aadeelnrx/DaVinciDriver/doc/pictures/Car_Prototype1_Top.JPG

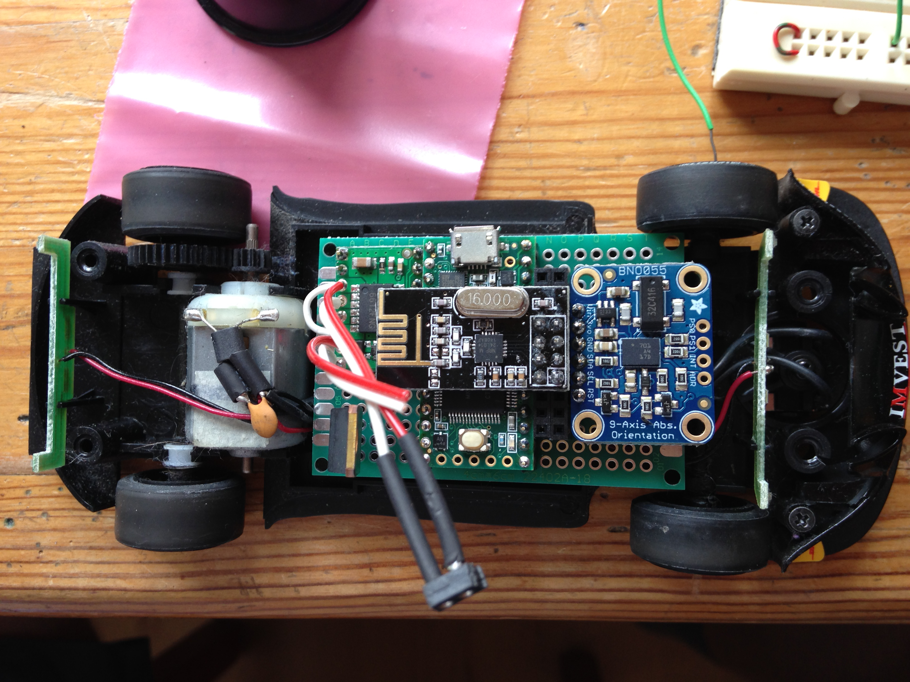
doc/pictures/Car_Prototype1_Top.JPG
