aadeelnrx/DaVinciDriver/doc/pictures/Car_Prototype2_TopSide.JPG

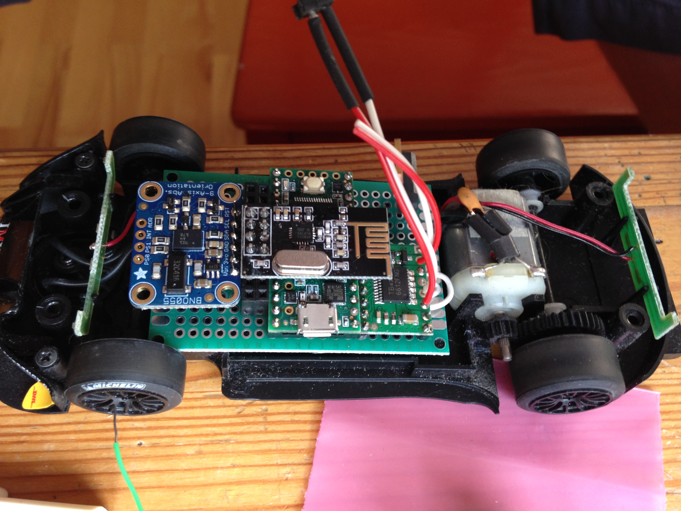
doc/pictures/Car_Prototype2_TopSide.JPG
