aadeelnrx/DaVinciDriver/doc/pictures/Teensy_31_Diode.JPG

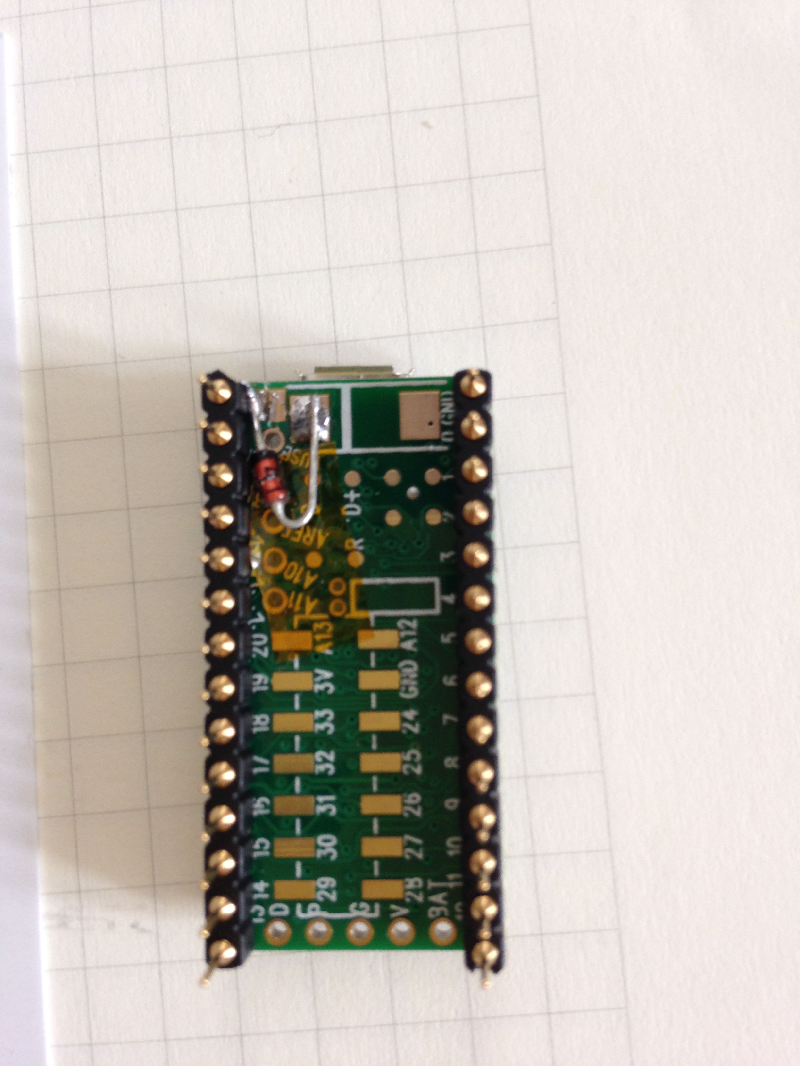
doc/pictures/Teensy_31_Diode.JPG
