aadeelnrx/DaVinciDriver/doc/Misc/accel-test-2-pwm-80-2.csv

Millis | ExTime | Distance | Speed | Acc_x | Acc_y | TrackVolt
10601 | 0 | 0 | 0 | 0.00 | 0.00 | 403
10621 | 0 | 1 | 1 | 0.00 | 0.00 | 415
10641 | 0 | 1 | 0 | 0.00 | 0.00 | 416
10661 | 0 | 2 | 1 | 0.00 | 0.00 | 408
10681 | 0 | 3 | 1 | 0.00 | 0.00 | 406
10701 | 0 | 6 | 3 | 0.00 | 0.00 | 394
10721 | 0 | 9 | 3 | 0.00 | 0.00 | 410
10741 | 0 | 13 | 4 | 0.00 | 0.00 | 404
10761 | 0 | 18 | 5 | 0.00 | 0.00 | 408
10781 | 0 | 24 | 6 | 0.00 | 0.00 | 406
10801 | 0 | 30 | 6 | 0.00 | 0.00 | 401
10821 | 0 | 37 | 7 | 0.00 | 0.00 | 405
10841 | 0 | 45 | 8 | 0.00 | 0.00 | 408
10861 | 0 | 54 | 9 | 0.00 | 0.00 | 407
10881 | 0 | 63 | 9 | 0.00 | 0.00 | 403
10901 | 0 | 72 | 9 | 0.00 | 0.00 | 404
10921 | 0 | 82 | 10 | 0.00 | 0.00 | 403
10941 | 0 | 93 | 11 | 0.00 | 0.00 | 399
10961 | 0 | 104 | 11 | 0.00 | 0.00 | 396
10981 | 0 | 116 | 12 | 0.00 | 0.00 | 394
11001 | 0 | 128 | 12 | 0.00 | 0.00 | 386
11021 | 0 | 141 | 13 | 0.00 | 0.00 | 391
11041 | 0 | 154 | 13 | 0.00 | 0.00 | 390
11061 | 0 | 167 | 13 | 0.00 | 0.00 | 388
11081 | 1 | 181 | 14 | -0.74 | -0.75 | 387
11101 | 1 | 196 | 15 | 1.87 | -0.54 | 406
11121 | 1 | 210 | 14 | -2.24 | -0.12 | 384
11141 | 1 | 226 | 16 | 1.35 | -0.82 | 396
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
