aadeelnrx/DaVinciDriver/doc/Misc/accel-test-2-pwm-80.csv

Millis | ExTime | Distance | Speed | Acc_x | Acc_y | TrackVolt
5601 | 0 | 0 | 0 | 0.00 | 0.00 | 394
5621 | 0 | 0 | 0 | 0.00 | 0.00 | 402
5641 | 0 | 0 | 0 | 0.00 | 0.00 | 403
5661 | 0 | 1 | 1 | 0.00 | 0.00 | 391
5681 | 0 | 2 | 1 | 0.00 | 0.00 | 390
5701 | 0 | 3 | 1 | 0.00 | 0.00 | 388
5721 | 0 | 6 | 3 | 0.00 | 0.00 | 385
5741 | 0 | 8 | 2 | 0.00 | 0.00 | 382
5761 | 0 | 12 | 4 | 0.00 | 0.00 | 380
5781 | 0 | 16 | 4 | 0.00 | 0.00 | 403
5801 | 0 | 22 | 6 | 0.00 | 0.00 | 408
5821 | 0 | 28 | 6 | 0.00 | 0.00 | 411
5841 | 0 | 35 | 7 | 0.00 | 0.00 | 410
5861 | 0 | 42 | 7 | 0.00 | 0.00 | 412
5881 | 0 | 50 | 8 | 0.00 | 0.00 | 412
5901 | 0 | 58 | 8 | 0.00 | 0.00 | 407
5921 | 0 | 67 | 9 | 0.00 | 0.00 | 408
5941 | 0 | 77 | 10 | 0.00 | 0.00 | 405
5961 | 0 | 88 | 11 | 0.00 | 0.00 | 408
5981 | 0 | 99 | 11 | 0.00 | 0.00 | 407
6001 | 0 | 111 | 12 | 0.00 | 0.00 | 408
6021 | 0 | 123 | 12 | 0.00 | 0.00 | 410
6041 | 0 | 136 | 13 | 0.00 | 0.00 | 410
6061 | 0 | 150 | 14 | 0.00 | 0.00 | 409
6081 | 1 | 164 | 14 | 1.31 | -0.48 | 405
6101 | 1 | 178 | 14 | -0.35 | -1.62 | 408
6121 | 1 | 193 | 15 | -0.81 | -1.49 | 403
6141 | 1 | 208 | 15 | 0.78 | -0.02 | 403
6161 | 1 | 224 | 16 | -2.76 | 0.09 | 407
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
