aadeelnrx/DaVinciDriver/doc/Misc/accel-test-3-pwm-128-2.csv

Millis | ExTime | Distance | Speed | Acc_x | Acc_y | TrackVolt
10601 | 0 | 0 | 0 | 0.00 | 0.00 | 366
10621 | 0 | 2 | 2 | 0.00 | 0.00 | 378
10641 | 0 | 4 | 2 | 0.00 | 0.00 | 385
10661 | 0 | 8 | 4 | 0.00 | 0.00 | 385
10681 | 0 | 13 | 5 | 0.00 | 0.00 | 371
10701 | 0 | 20 | 7 | 0.00 | 0.00 | 374
10721 | 0 | 28 | 8 | 0.00 | 0.00 | 375
10741 | 0 | 37 | 9 | 0.00 | 0.00 | 369
10761 | 0 | 47 | 10 | 0.00 | 0.00 | 369
10781 | 0 | 60 | 13 | 0.00 | 0.00 | 370
10801 | 0 | 73 | 13 | 0.00 | 0.00 | 362
10821 | 0 | 87 | 14 | 0.00 | 0.00 | 365
10841 | 0 | 102 | 15 | 0.00 | 0.00 | 366
10861 | 0 | 119 | 17 | 0.00 | 0.00 | 369
10881 | 0 | 136 | 17 | 0.00 | 0.00 | 368
10901 | 0 | 153 | 17 | 0.00 | 0.00 | 367
10921 | 0 | 173 | 20 | 0.00 | 0.00 | 362
10941 | 0 | 193 | 20 | 0.00 | 0.00 | 367
10961 | 0 | 214 | 21 | 0.00 | 0.00 | 369
10981 | 0 | 236 | 22 | 0.00 | 0.00 | 356
11001 | 0 | 259 | 23 | 0.00 | 0.00 | 362
11021 | 0 | 283 | 24 | 0.00 | 0.00 | 363
11041 | 0 | 308 | 25 | 0.00 | 0.00 | 363
11061 | 0 | 333 | 25 | 0.00 | 0.00 | 380
11081 | 1 | 358 | 25 | -1.90 | -2.83 | 365
11101 | 1 | 385 | 27 | 2.29 | -1.44 | 365
11121 | 1 | 412 | 27 | 0.24 | -1.58 | 362
11141 | 1 | 439 | 27 | 0.68 | 0.42 | 363
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
