aadeelnrx/DaVinciDriver/doc/Misc/PID_Measurements/CapturePID_15_1_0.JPG

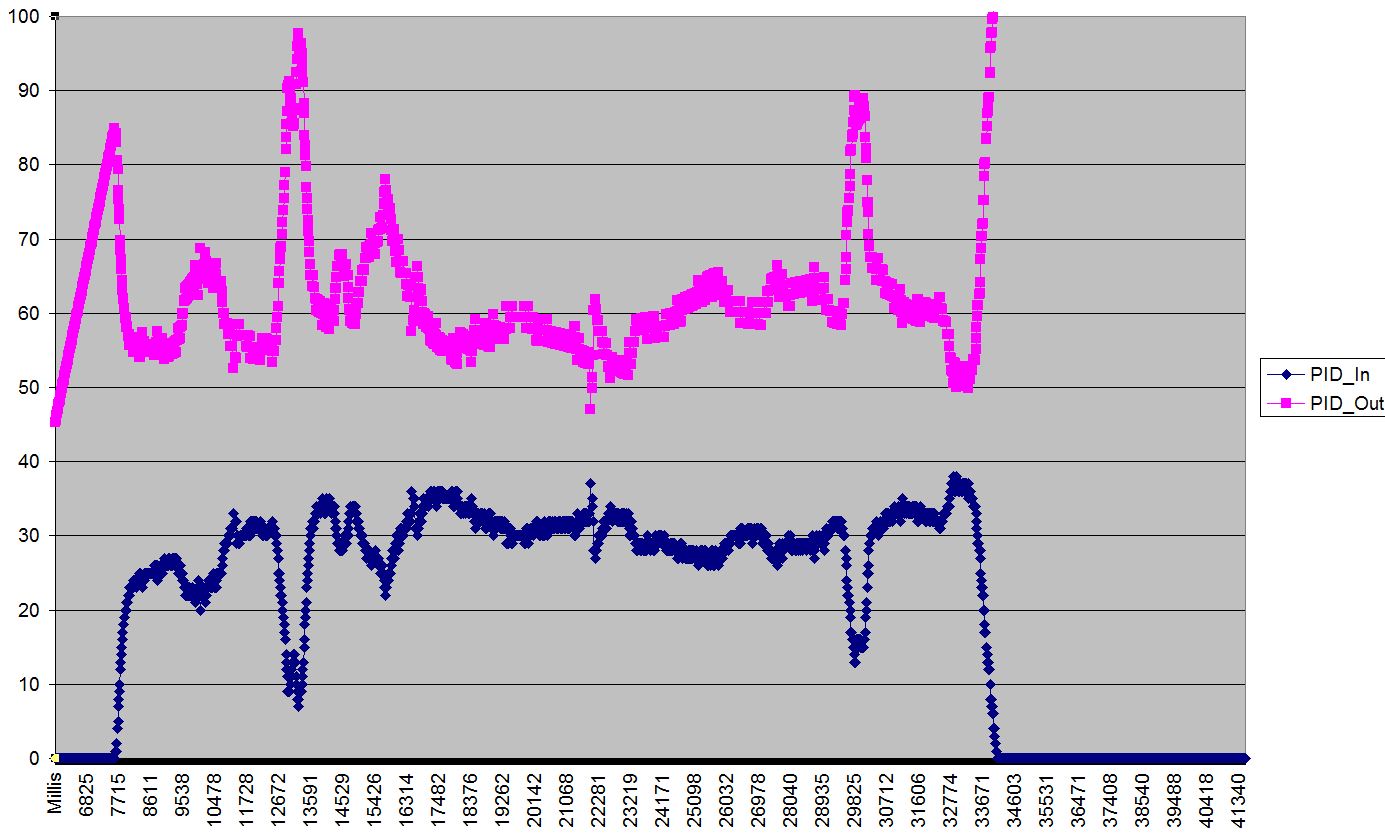
doc/Misc/PID_Measurements/CapturePID_15_1_0.JPG
