aadeelnrx/DaVinciDriver/doc/Misc/PID_Measurements/CapturePID_25_2_0.JPG

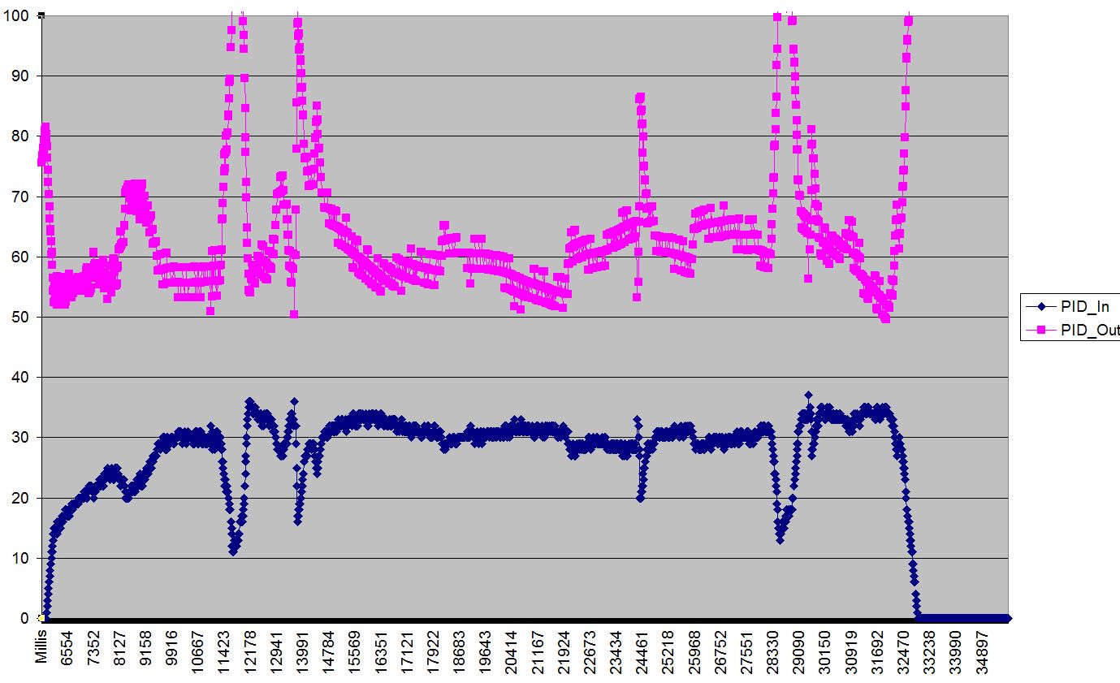
doc/Misc/PID_Measurements/CapturePID_25_2_0.JPG
