aadeelnrx/DaVinciDriver/doc/Misc/PID_Measurements/CapturePID_25_5_0.JPG

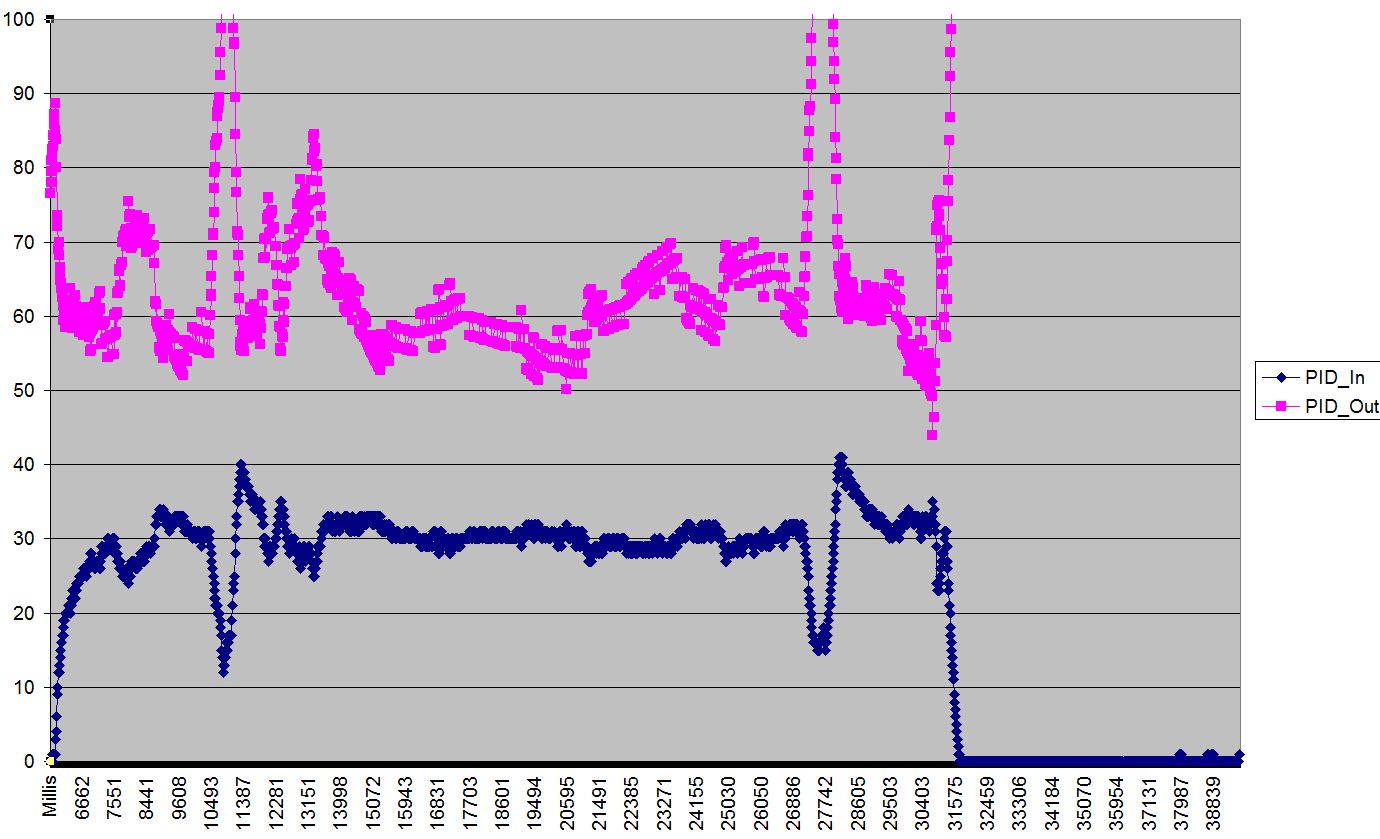
doc/Misc/PID_Measurements/CapturePID_25_5_0.JPG
