aadeelnrx/DaVinciDriver/doc/Misc/PID_Measurements/CapturePID_25_10_0001.JPG

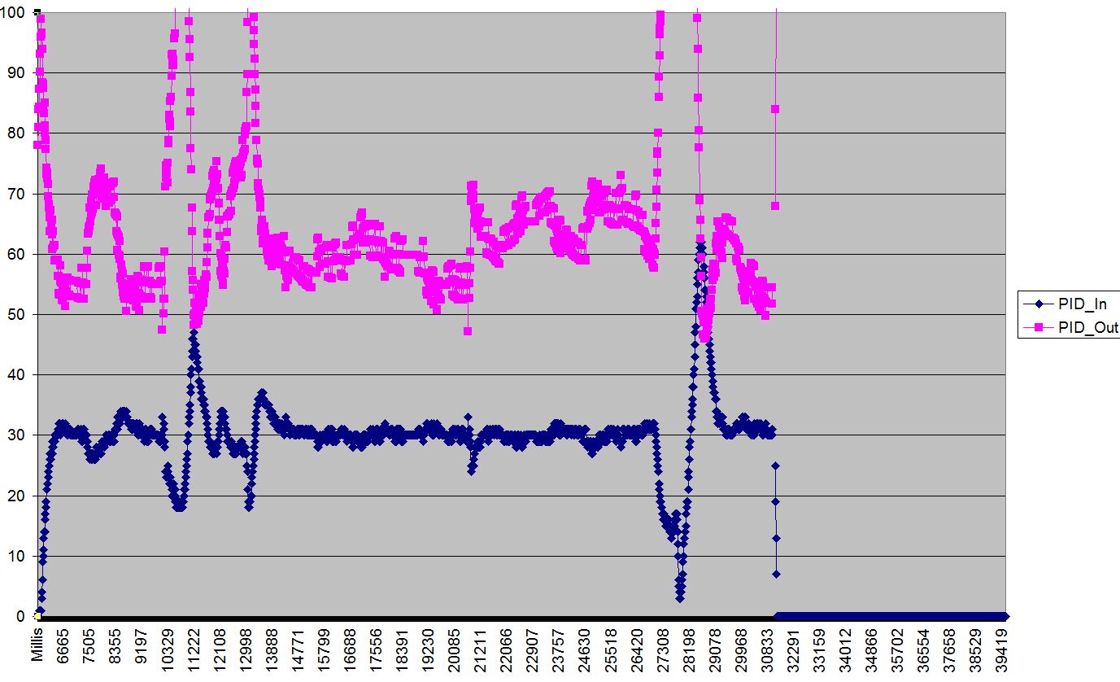
doc/Misc/PID_Measurements/CapturePID_25_10_0001.JPG
