aadeelnrx/DaVinciDriver/doc/Misc/PID_Measurements/CapturePID_25_10_01.JPG

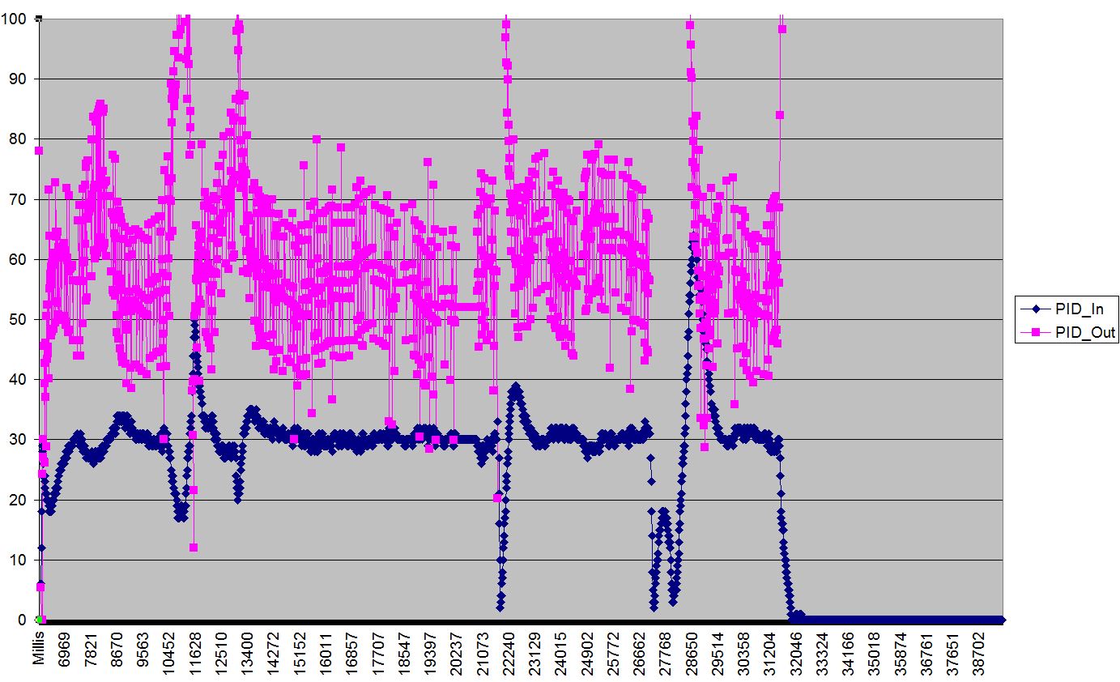
doc/Misc/PID_Measurements/CapturePID_25_10_01.JPG
