aadeelnrx/DaVinciDriver/doc/Misc/PID_Measurements/CapturePID_075_1_001_30ms.JPG

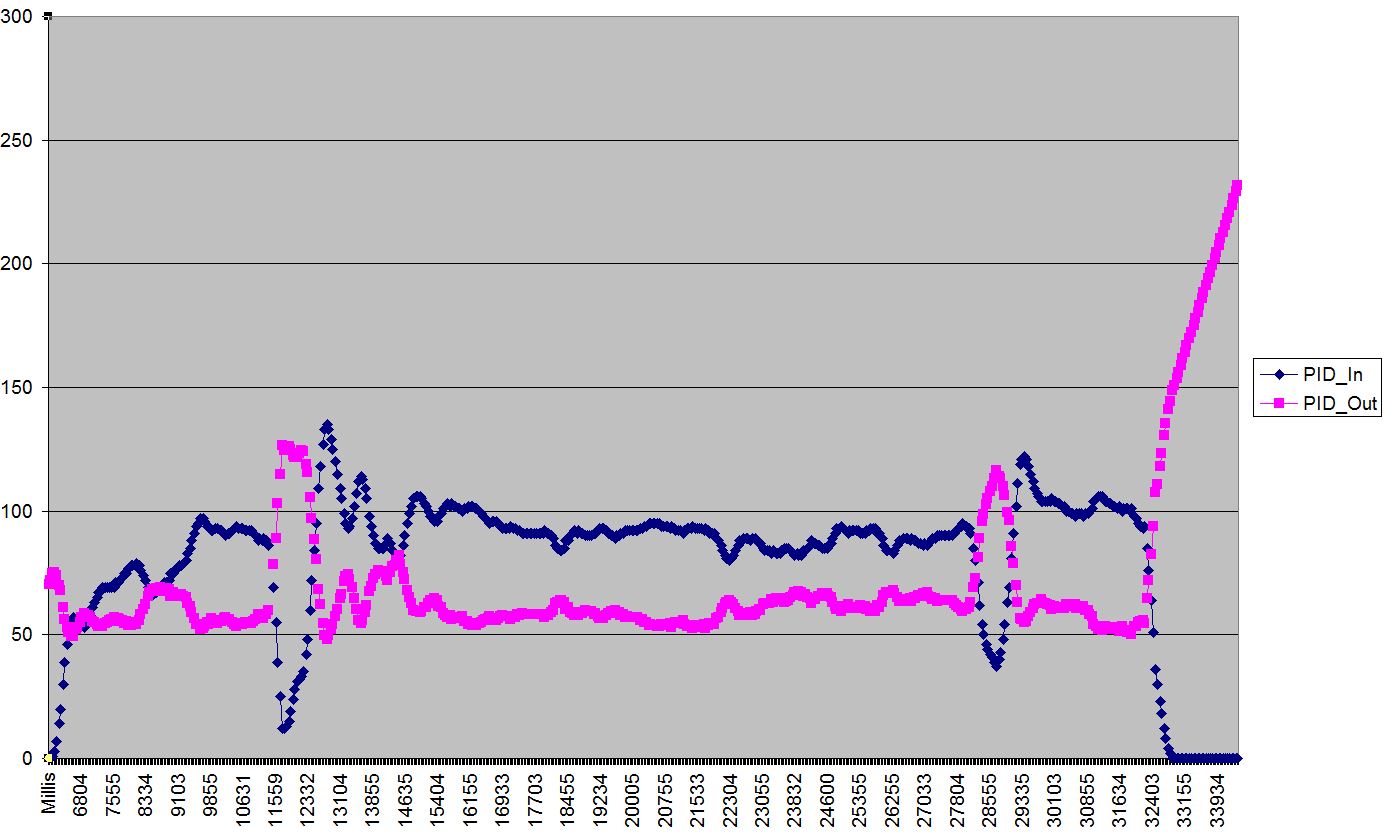
doc/Misc/PID_Measurements/CapturePID_075_1_001_30ms.JPG
